picafe/bicolor-matrix-v2/assets/adapter-board-v2-sch.png

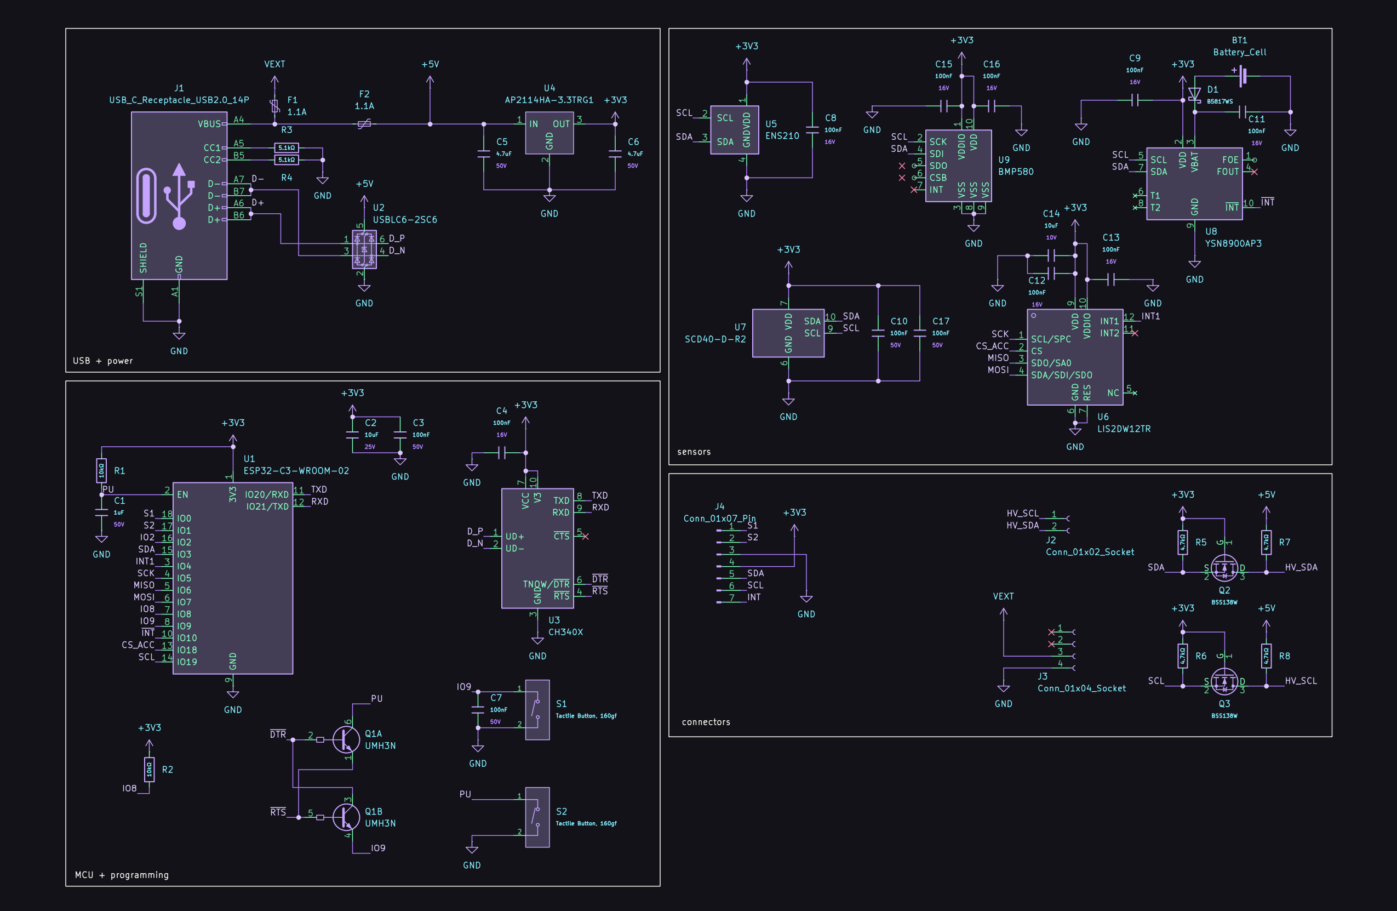
assets/adapter-board-v2-sch.png
