picafe/bicolor-matrix-v2/assets/kicad_ezY7QcU7CC.png

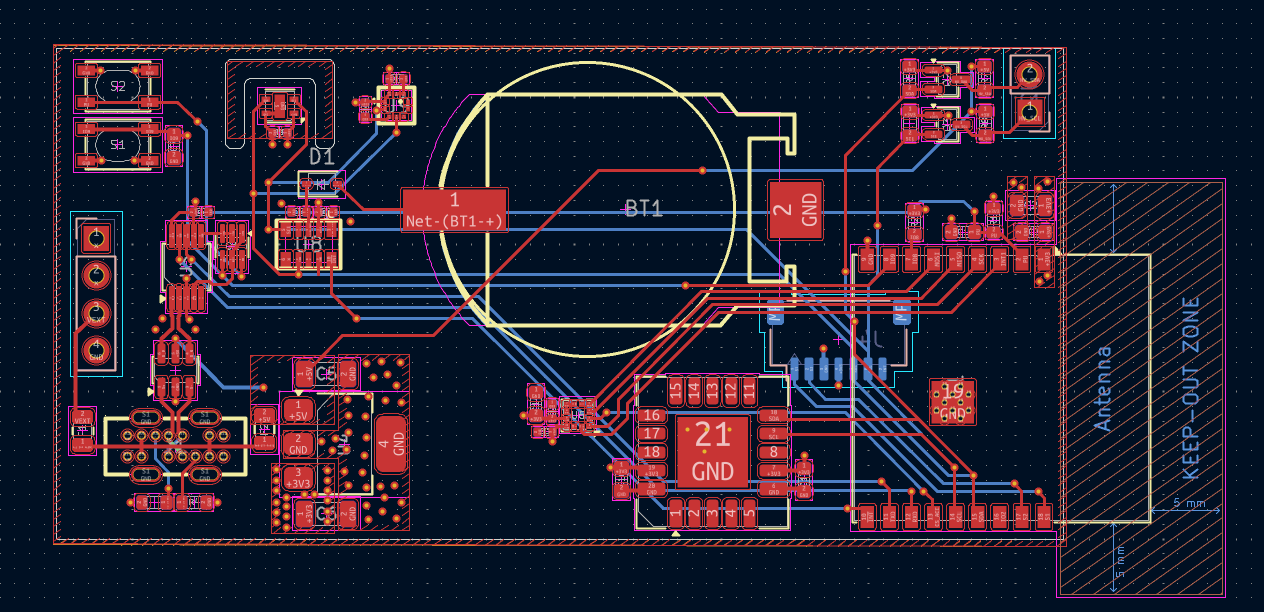
assets/kicad_ezY7QcU7CC.png
